ulogix-team/ulogix-manufacturing/proceso/diagramas/Diagrama_DAP_2_(Light).png

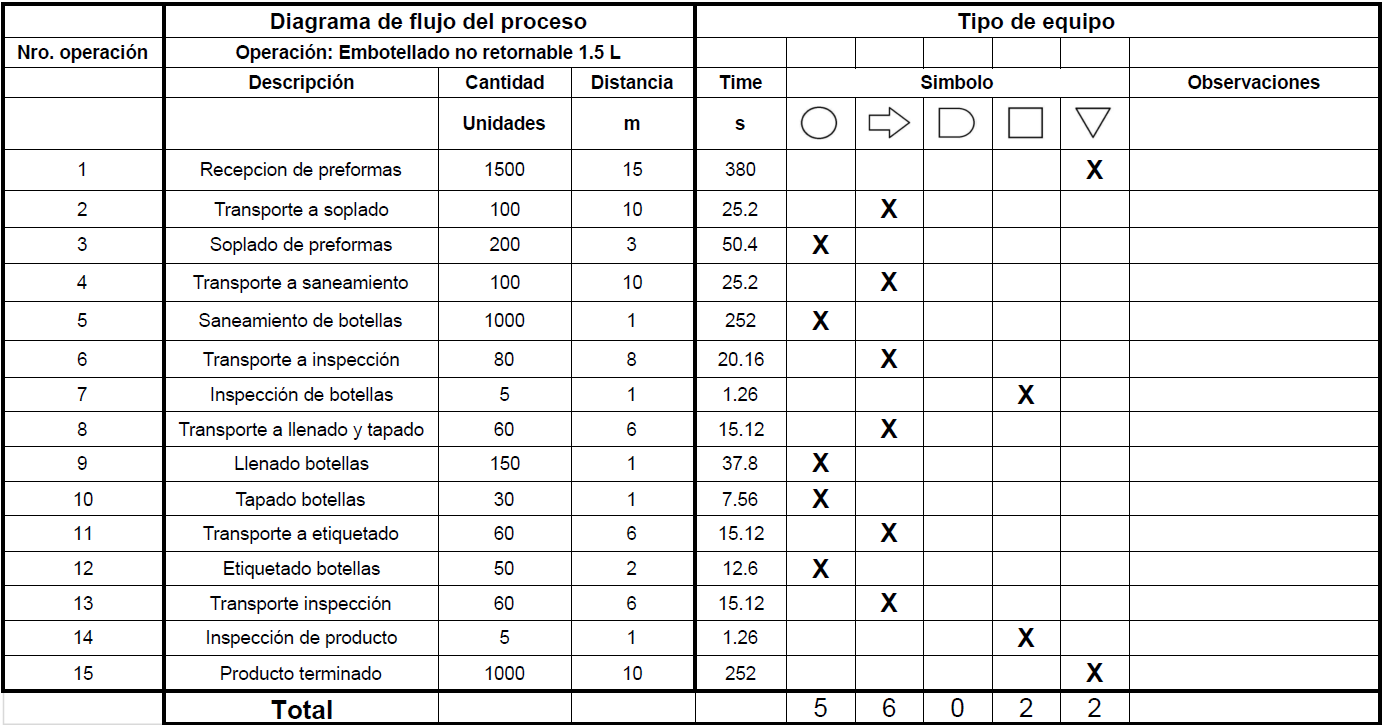
proceso/diagramas/Diagrama_DAP_2_(Light).png
