ulogix-team/ulogix-manufacturing/proceso/vsm/Diagrama_VSM_1_(Dark).png

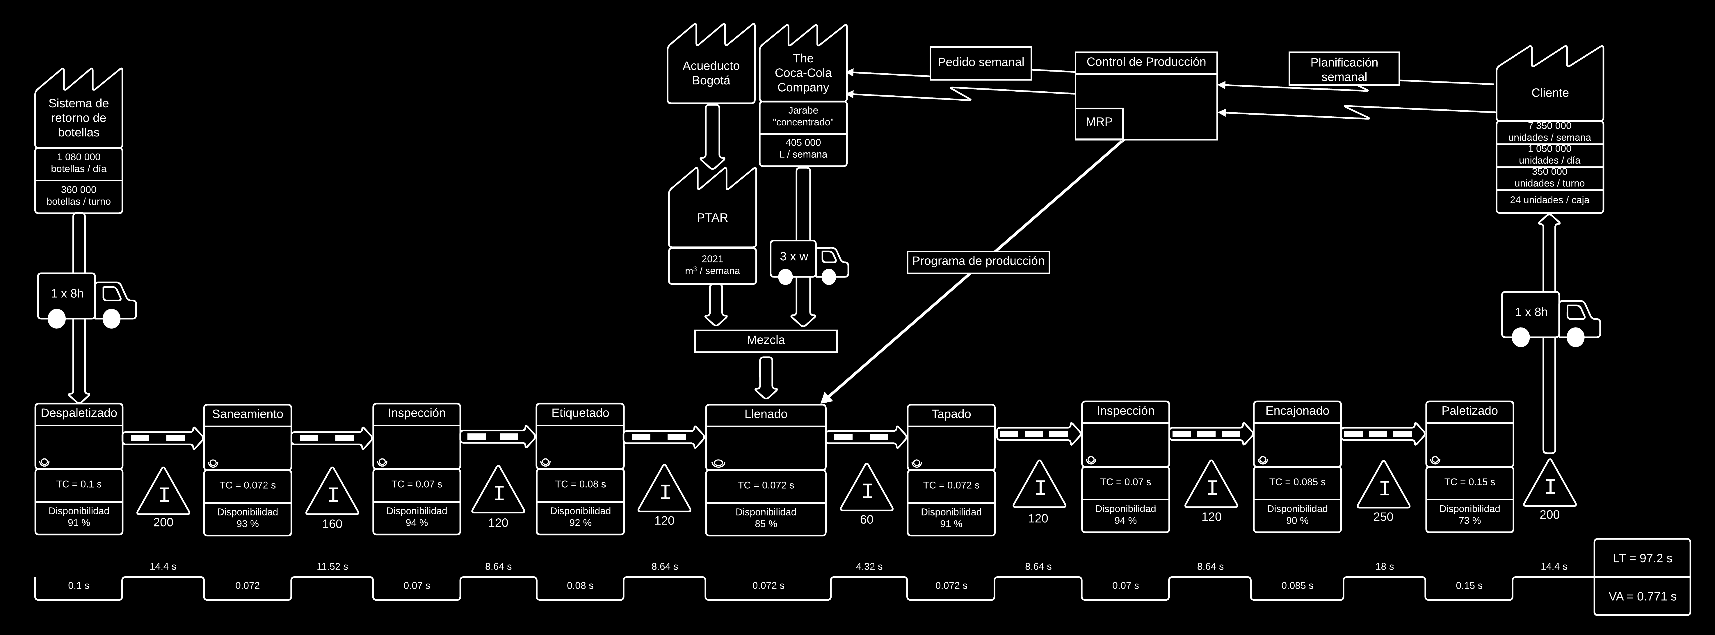
proceso/vsm/Diagrama_VSM_1_(Dark).png
